wsaudio/Bizcard/Software/Src/HH.c

#include "HH.h"

uint8_t HHDecayTime[noOfHHs] = {defaultHHCloseDecay, defaultHHOpenDecay};
uint32_t HHAmpInc[noOfHHs];
uint32_t HHAmpValue[noOfHHs];
uint32_t HHAmpPos[noOfHHs];
uint32_t HHAmpLen[noOfHHs];
uint8_t HHNoteOn[noOfHHs] = {0, 0};
uint16_t HHLutPos[noOfHHs] = {0, 0};

const int8_t HHLUT[HHLUTSize] = { 
-29,
-45,
-6,
10,
3,
3,
7,
4,
20,
20,
-25,
-52,
-10,
41,
43,
12,
-32,
-51,
-21,
33,
29,
-12,
-7,
28,
7,
-38,
-31,
2,
24,
36,
35,
-26,
-68,
-39,
30,
54,
6,
9,
26,
-48,
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
};

void initHHParams(void)
{
	for (uint8_t i = 0; i < noOfHHs; i++)
		calcHHDecayTim(i);
}

void changeHHDecayTime(uint8_t instrument, uint8_t newTime)
{
	//Check range
	if (instrument < noOfHHs)
	{
		//Increase or decrease time
		switch (newTime)
		{
			//Decrease time
			case 0:
				if (HHDecayTime[instrument] > kickDecMin)
					HHDecayTime[instrument]--;
				break;
			//Increase time
			case 1:
				if (HHDecayTime[instrument] < kickDecMax)
					HHDecayTime[instrument]++;
				break;
			default:
				break;
		}
		
		calcHHDecayTim(instrument);
	}
}

void calcHHDecayTim(uint8_t instrument)
{
	double decayTime;

	if (instrument == 0)
		decayTime = (double)HHDecayTime[instrument] / 10 * ClosedHHMaxDecayTime;
	else
		decayTime = (double)HHDecayTime[instrument] / 10 * OpenHHMaxDecayTime;
	
	//Convert to increment value and scale for amp decay LUT
	double inc = ampDecLUTSize * decayTime / fs;
	
	HHAmpLen[instrument] = fs * decayTime;
	
	//Convert to fixed point increment value
	HHAmpInc[instrument] = inc * pow(2, fixedPointPos);
}

void setHHNoteOn(uint8_t instrument)
{
	//Check range
	if (instrument < noOfHHs)
	{
		HHAmpValue[instrument] = fp(255);
		HHNoteOn[instrument] = 1;
		HHAmpPos[instrument] = 0;
		
		//Cancel other HH
		HHNoteOn[!instrument] = 0;
	}
}

void incHHLUTPos(uint8_t instrument)
{
	//Check range
	if (instrument < noOfHHs)
	{
		HHLutPos[instrument]++;
		
		if (HHLutPos[instrument] >= HHLUTSize)
			HHLutPos[instrument] -= HHLUTSize;
	}
}

uint8_t getCurrentHHAmp(uint8_t instrument)
{
	//Check range
	if (instrument < noOfHHs)
	{
		HHAmpPos[instrument]++;
		
		//During note
		if (HHAmpPos[instrument] < HHAmpLen[instrument])
		{
			HHAmpValue[instrument] -= HHAmpInc[instrument];
			return ufp(HHAmpValue[instrument]);
		}
		//Note finished
		else
		{
			HHNoteOn[instrument] = 0;
			return 0;
		}
	}
	else
		return 0;
}

void HHGenerateBuffer(uint8_t instrument, int8_t *buffer, uint16_t nFrames)
{
	uint8_t amp;
	int32_t val;
	
	//Check range
	if ((instrument < noOfHHs) && (HHNoteOn[instrument]))
	{
		for (uint16_t i = 0; i < nFrames; i++)
		{
			amp = getCurrentHHAmp(instrument);
			
			val = amp * HHLUT[HHLutPos[instrument]];
			
			incHHLUTPos(instrument);
			
			buffer[i] = val / 256;
		}
	}
	else
		memset(buffer, 0, nFrames * sizeof(int8_t));
}
