wsaudio/Bizcard/Software/Src/LUTs.c

#include "LUTs.h"

uint32_t randPos = 0;
const int8_t sinLUTData[sinLUTSize] = 
{ 0,
1,
2,
3,
4,
5,
6,
7,
8,
9,
10,
11,
12,
13,
14,
15,
16,
17,
18,
19,
20,
21,
22,
23,
24,
25,
26,
27,
28,
29,
30,
31,
32,
33,
34,
35,
36,
37,
38,
39,
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

const uint8_t pitchDecLUTData[pitchDecLUTSize] = 
{ 255,
240,
226,
212,
200,
188,
177,
167,
157,
148,
139,
131,
124,
116,
110,
103,
97,
91,
86,
81,
76,
72,
68,
64,
60,
56,
53,
50,
47,
44,
42,
39,
37,
35,
33,
31,
29,
27,
26,
24,
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

const uint8_t ampDecLUTData[ampDecLUTSize] = 
{ 255,
251,
248,
245,
243,
240,
237,
234,
231,
228,
226,
223,
220,
218,
215,
212,
210,
207,
205,
203,
200,
198,
195,
193,
191,
188,
186,
184,
182,
180,
177,
175,
173,
171,
169,
167,
165,
163,
161,
159,
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


/*sinLUT
Returns linear interpolated sine value
pos: position in sine LUT
return: sine value at position
*/
int8_t sinLUT(uint32_t pos)
{
	uint16_t intPos; 
	
	//Check range
	if (pos < sinLUTLimit)
	{
		//Remove decimal places for integer position
		intPos = ufp(pos);
		
		return sinLUTData[intPos];
	}
		
	else
		return 0;
}

/*pitchDecLUT
Returns rounded pitch value
pos: position in LUT
return: value at position
*/
uint8_t pitchDecLUT(uint32_t pos)
{
	uint16_t intPos; 
	
	//Check range
	if (pos < pitchDecLUTLimit)
	{
		//Remove decimal places for integer position
		intPos = ufp(pos);
		
		//Add samples and remove decimal places
		return pitchDecLUTData[intPos];
	}
		
	else
		return 0;
}

/*ampDecLUT
Returns rounded amp value
pos: position in LUT
return: value at position
*/
uint8_t ampDecLUT(uint32_t pos)
{
	uint16_t intPos; 
	
	//Check range
	if (pos < ampDecLUTLimit)
	{
		//Remove decimal places for integer position
		intPos = ufp(pos);
		
		//Add samples and remove decimal places
		return ampDecLUTData[intPos];
	}
		
	else
		return 0;
}

/*rnd
Returns random 8 bit value, used for noise generation
Return: random value
*/
uint8_t rnd()
{
	randPos += TIM3->CNT;
	randPos += 941;
	
	return randPos & 0xFF;
}
